bbs-tghs/LED-Cube/software/MUX_Test/timer.h

#ifndef _TIMER_
#define _TIMER_
/**
  @file timer.h
  
  @brief  Alle Routinen für den Timerbetrieb
  
  Die Bibliothek stellt eine Reihe von Flags zur Verfügung, die in bestimmten Intervallen gesetzt werden. 
  Der Benutzer kann diese Flags in seinem Hauptprogramm prüfen und eine Aktion ausführen, wenn es gesetzt ist. 
  Der Benutzer muss das Flag wieder löschen. Auch dazu werden Funktionen bereitgestellt.
  
  Der Timerinterrupt setzt in der globalen Variablen timerFlags je ein Flag für das Auftreten des entsprechenden Events.
  Die Flags müssen nach der Bearbeitung des Events vom Hauptprogramm gelöscht werden.
  Dadurch kann die Eventbearbeitung auch länger dauern als die Interruptzeit erlauben würde (asynchron)

  Synchrone Verarbeitung ist über die DoXXX Prozeduren möglich.
  
  Timer0 -> internes Taktraster
  
  Created: 27.05.2011 08:27:44

  @author  Michael Busser  

*/


struct TFlagsTimer {
  unsigned bMilli:1;    //- Flag für 1/1000 Sekunde vergangen
  unsigned b2Milli:1;	//- Flag für 2/1000 Sekunde vergangen
  unsigned b5Milli:1;	//- Flag für 5/1000 Sekunde vergangen
  unsigned bCenti:1;    //- Flag für 1/100 Sekunde
  unsigned bDezi:1;     //- Flag für 1/10 Sekunde
  unsigned bSek:1;      //- Flag für 1 Sekunde
  unsigned b10Sek:1;    //- Flag für 10 Sekunden sind vergangen
  unsigned bMin:1;      //- Flag für 1 Minute ist vergangen
};


union TTimer {
  unsigned char         all;
  struct   TFlagsTimer  flags;
};


typedef void (*timer_callback_t) (void);		//Event Callback-Funktion, es werden keine Parameter übergeben

//-----------------------------------------------------------
// Flags markieren das Event
//-----------------------------------------------------------
/**
 @brief Die Variable timerflags ist eine Struktur, in der jedes Bit über einen Namen angesprochen werden kann.
        Der Timerinterrupt setzt das Bit, wenn die zugeordnete Zeit abgelaufen ist.
		timerFlags.b5Mill wird also alle 5 Millisekunden gesetzt. Das Flag kann jetzt einfach geprüft werden.
		Das flag muss wieder gelöscht werden. Dazu gibt es für jedes Flag eine Funktion mit ähnlichem Namen.
		Ein Aufruf von timerClear5Milli() löscht also das Flag für den 5-Millisekunden-Takt.
*/
volatile union TTimer timerFlags;

void timerInit( void );
void timerClearAll( void );
void timerClearMilli( void );
void timerClear2Milli( void );
void timerClear5Milli( void );
void timerClearCenti( void );
void timerClearDezi( void );
void timerClearSek( void );
void timerClear10Sek( void );
void timerClearMin( void );

void register_Timer_Callback_1MS( timer_callback_t cbf );

#endif	//_TIMER_
